hugokernel/Bleuette/export/img/BleuettePi_board.png

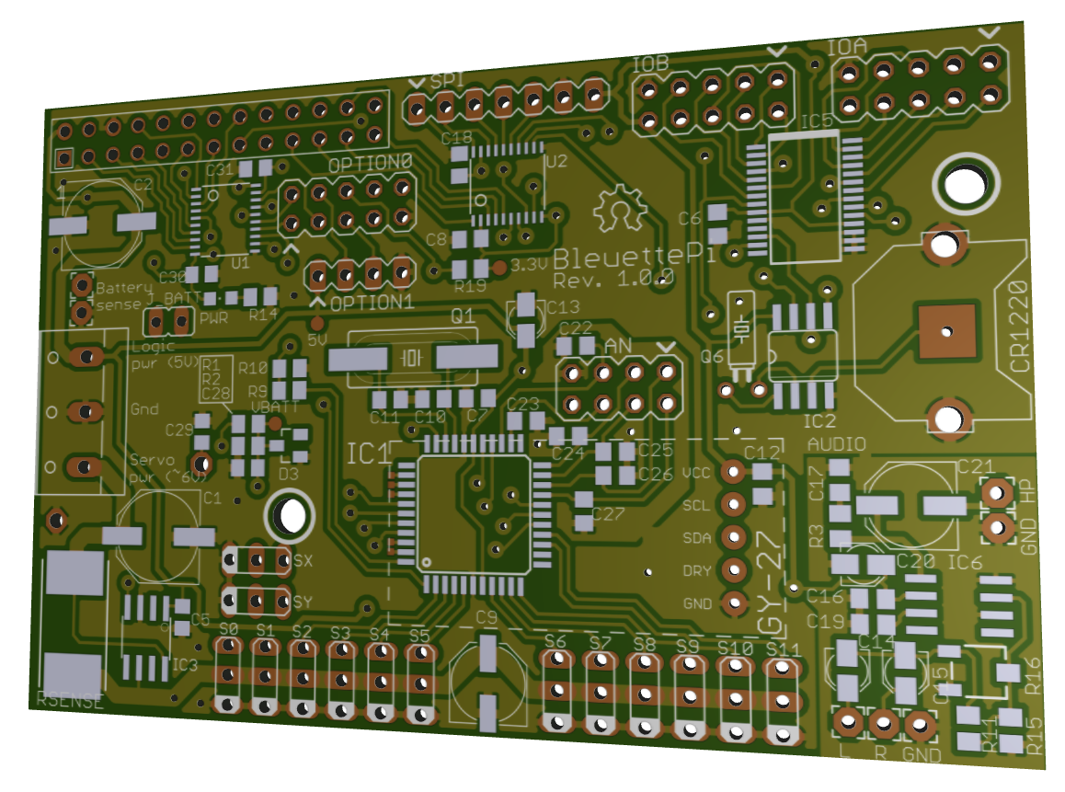
export/img/BleuettePi_board.png
