hugokernel/Bleuette/export/img/BleuettePi_pcb.png

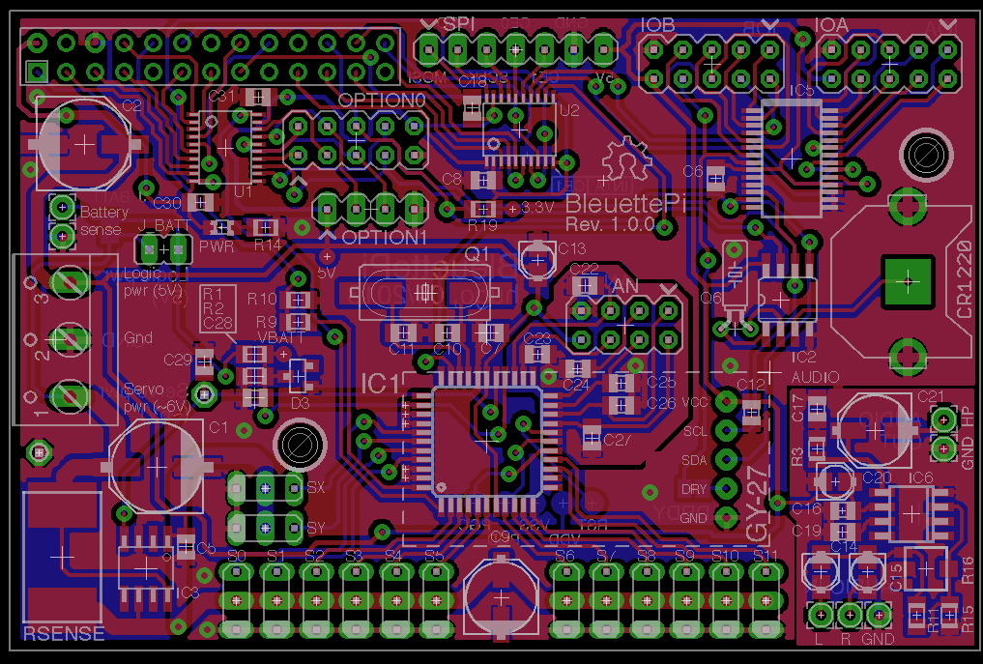
export/img/BleuettePi_pcb.png
