hugokernel/Bleuette/export/img/body.png

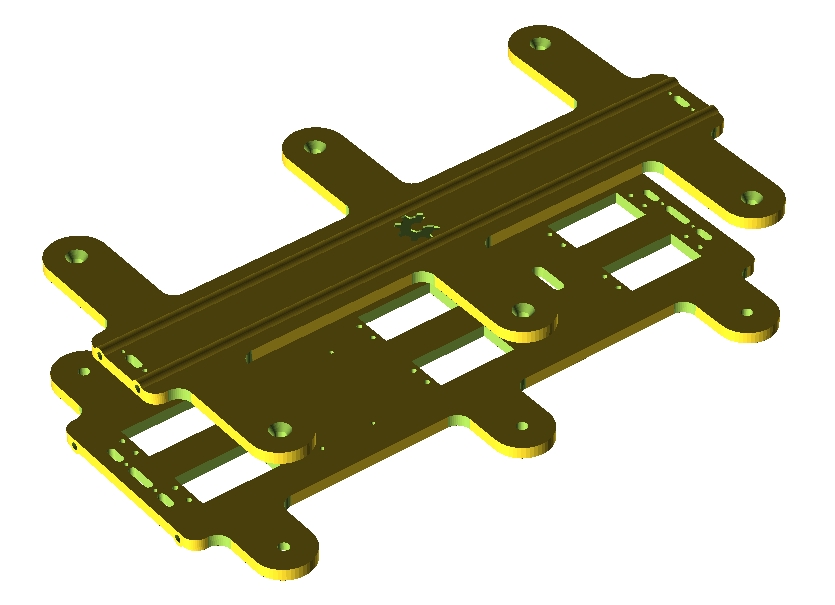
export/img/body.png
