hugokernel/Bleuette/export/img/body_base.png

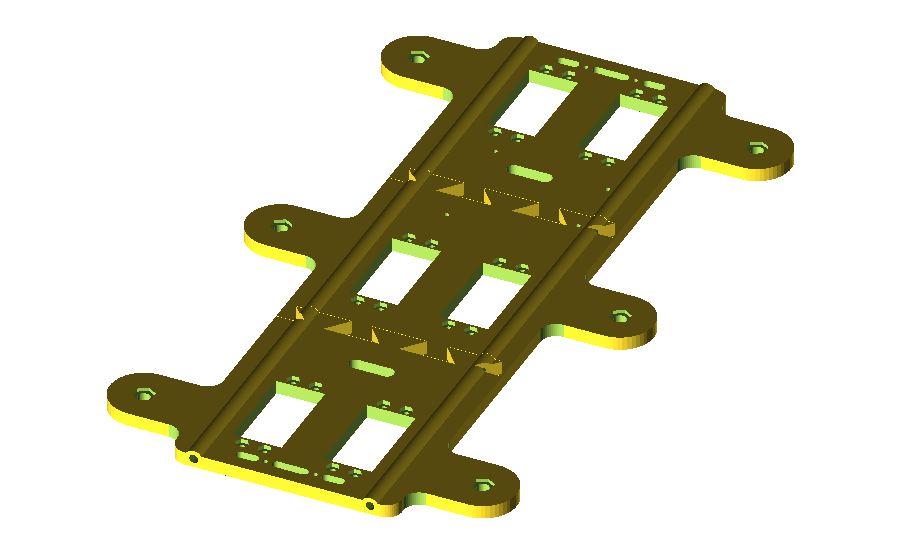
export/img/body_base.png
