hugokernel/Bleuette/export/img/body_base_ortho.png

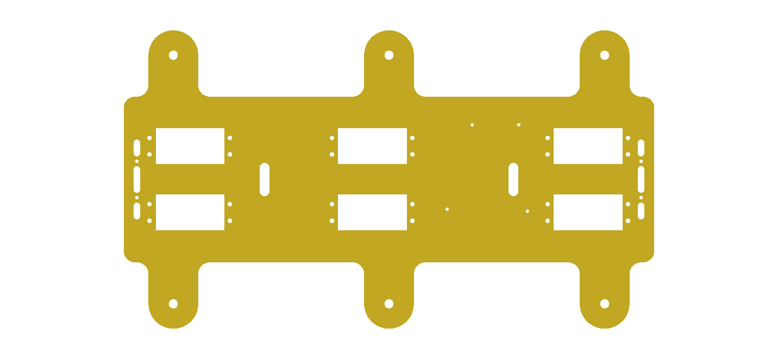
export/img/body_base_ortho.png
