hugokernel/Bleuette/export/img/body_support.png

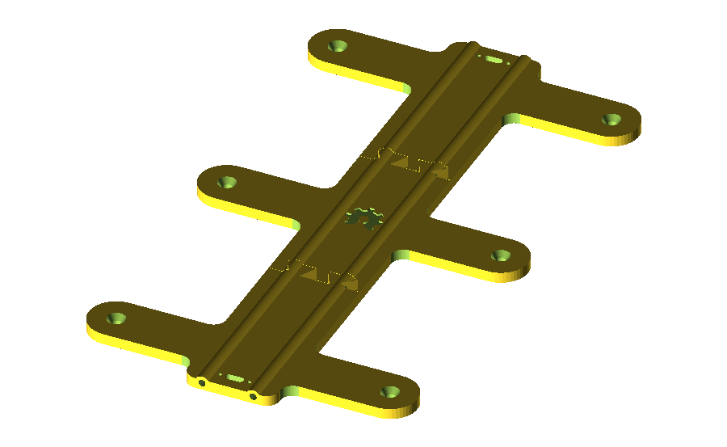
export/img/body_support.png
