hugokernel/Bleuette/export/img/body_support_ortho.png

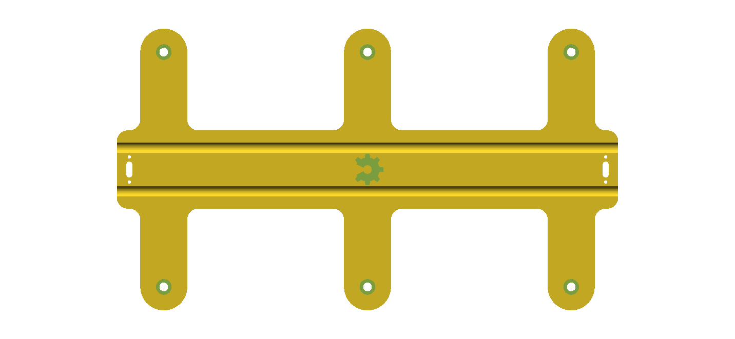
export/img/body_support_ortho.png
