hugokernel/Bleuette/export/img/elec_board.png

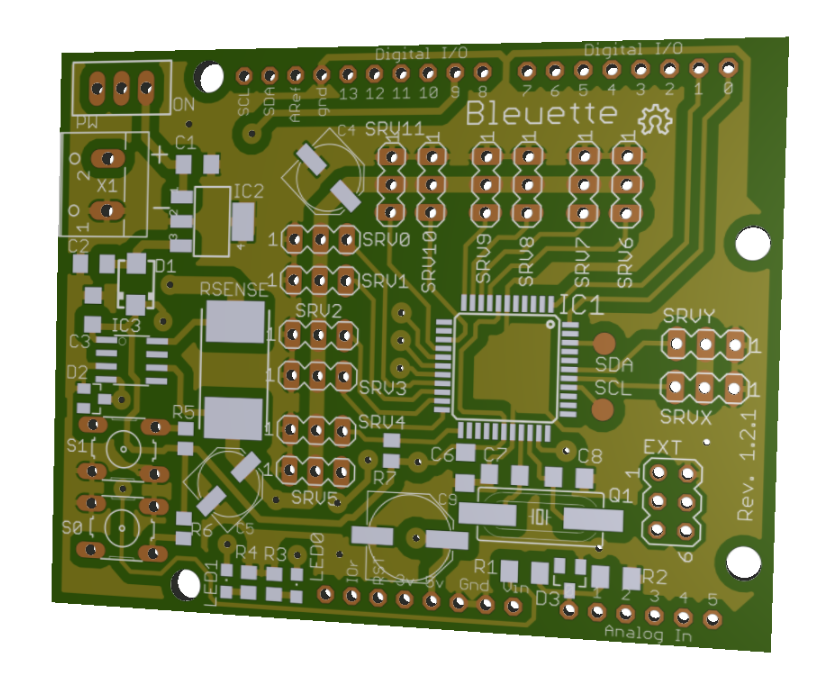
export/img/elec_board.png
