hugokernel/Bleuette/export/img/elec_board_1.2.1.png

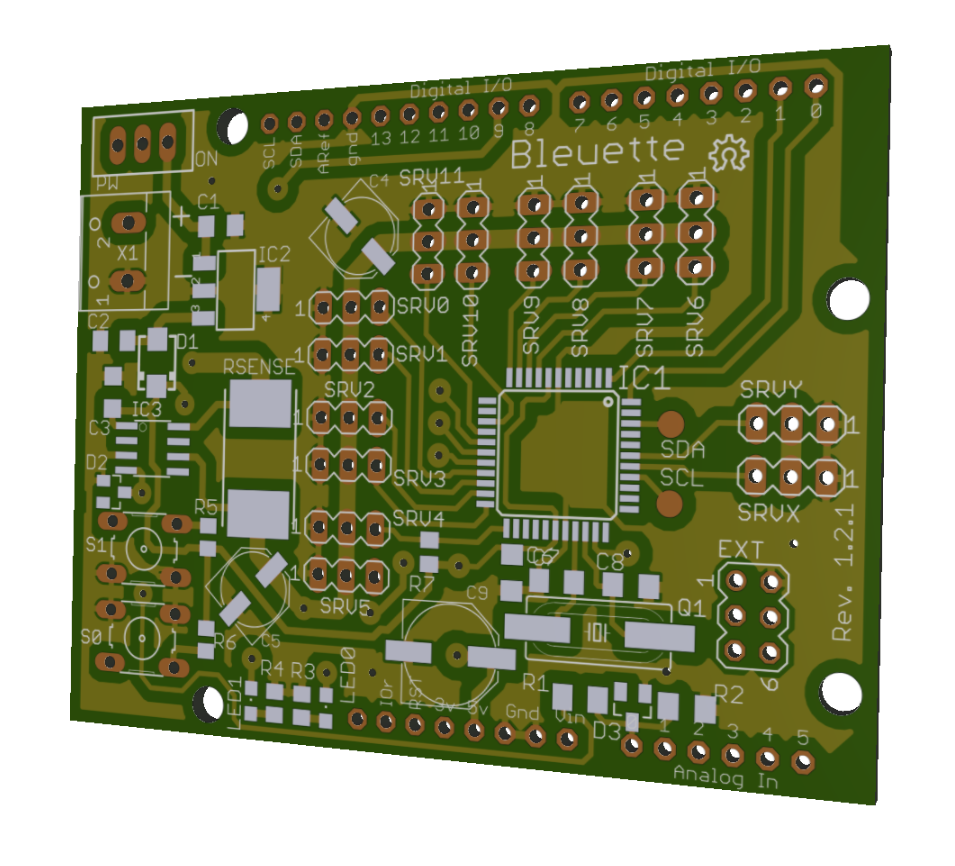
export/img/elec_board_1.2.1.png
