hugokernel/Bleuette/export/img/elec_pcb.png

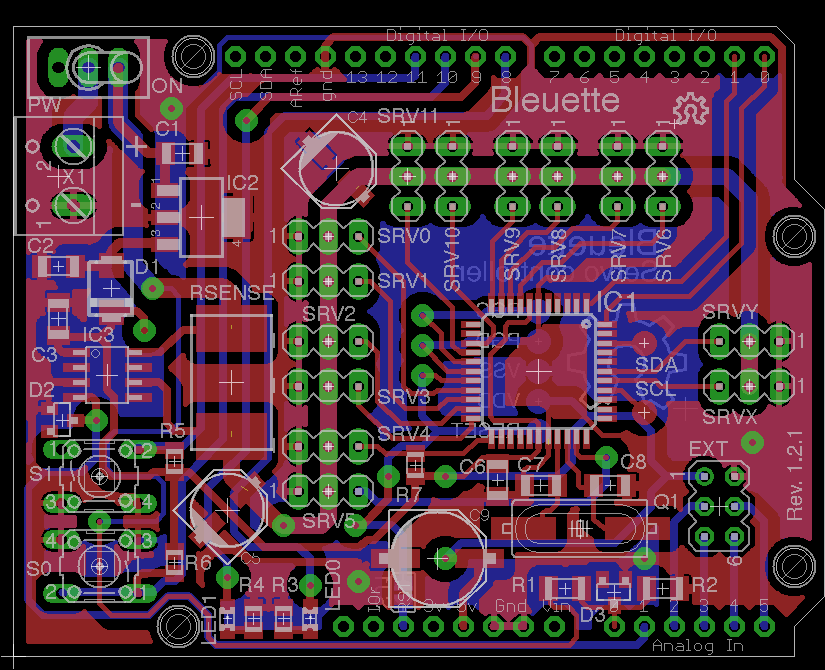
export/img/elec_pcb.png
