hugokernel/Bleuette/export/img/leg_holder.png

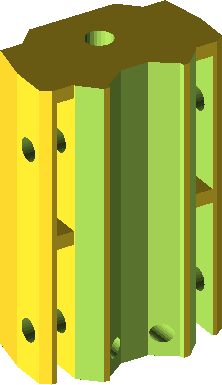
export/img/leg_holder.png
