hugokernel/Bleuette/export/img/leg_holder_pieces.png

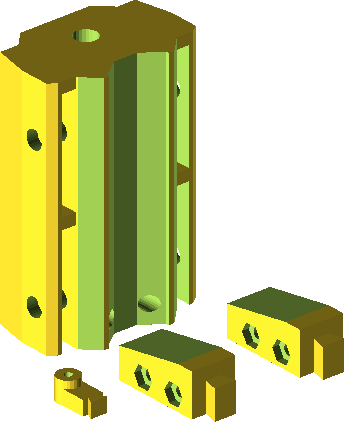
export/img/leg_holder_pieces.png
