hugokernel/Bleuette/export/img/leg_long.png

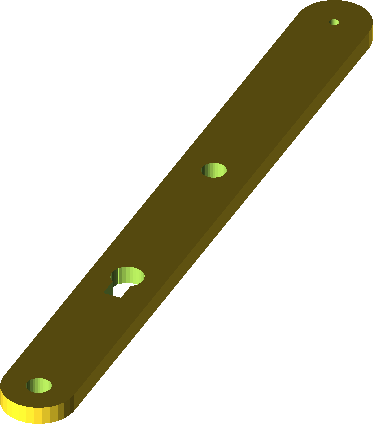
export/img/leg_long.png
