hugokernel/Bleuette/export/img/leg_main.png

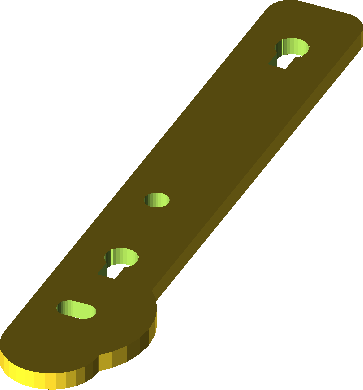
export/img/leg_main.png
