hugokernel/Bleuette/export/img/leg_sensor.png

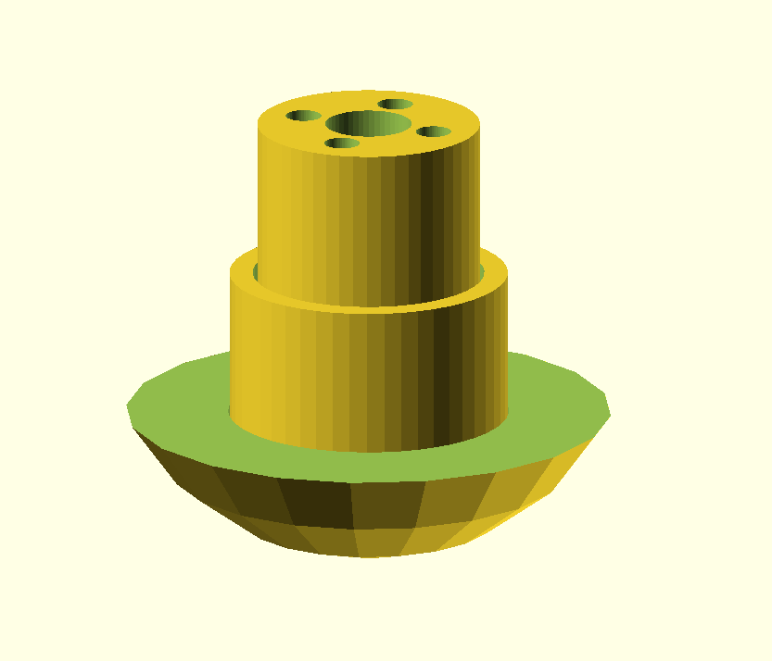
export/img/leg_sensor.png
