hugokernel/Bleuette/export/img/leg_short.png

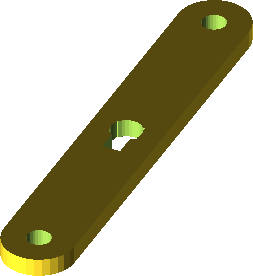
export/img/leg_short.png
