hugokernel/Bleuette/export/img/pcb_1.0.2/00.jpeg

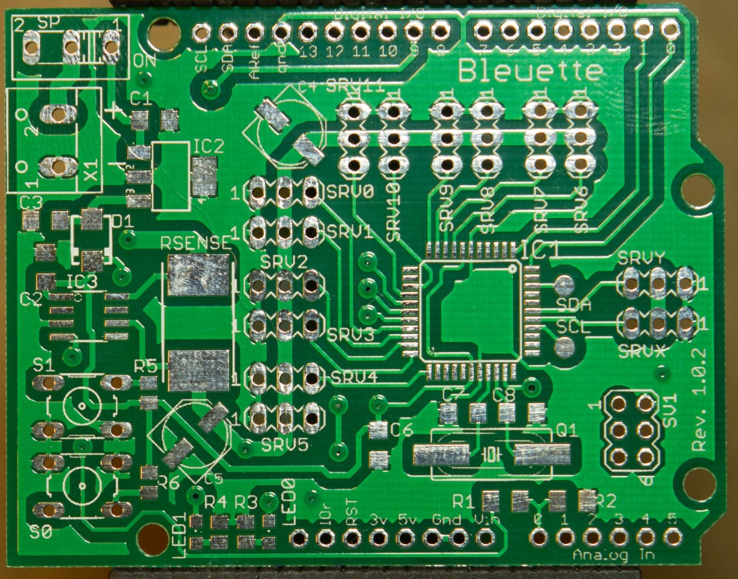
export/img/pcb_1.0.2/00.jpeg
