hugokernel/Bleuette/export/img/pcb_1.0.2/03.jpeg

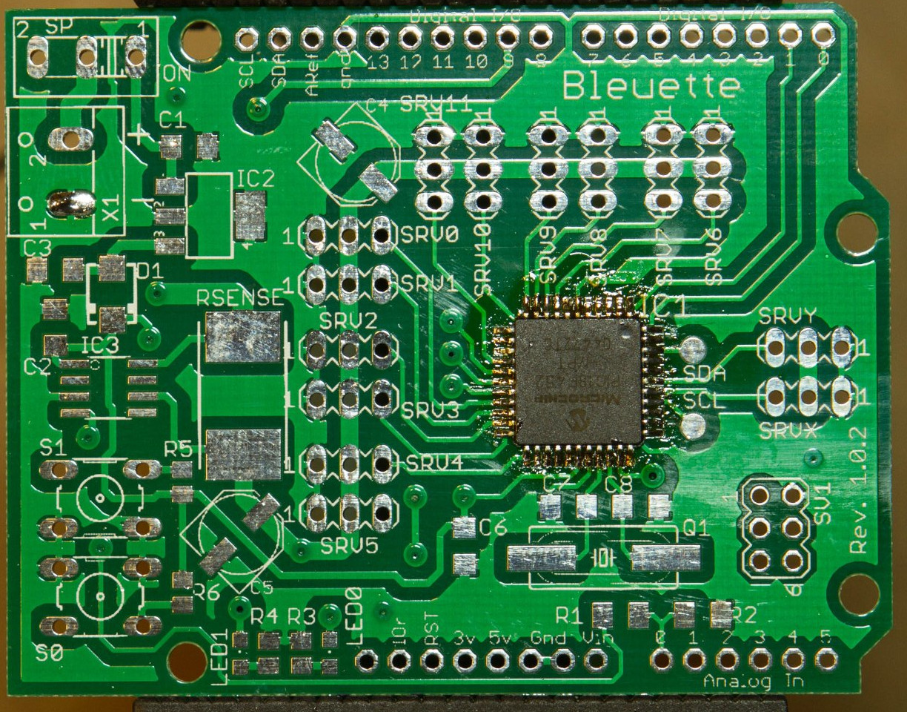
export/img/pcb_1.0.2/03.jpeg
