hugokernel/Bleuette/export/img/pcb_1.0.2/04.jpeg

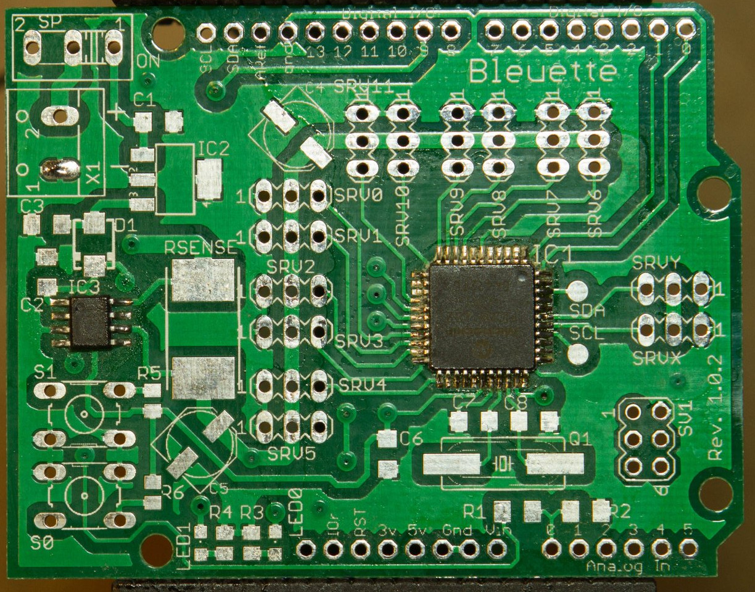
export/img/pcb_1.0.2/04.jpeg
