hugokernel/Bleuette/export/img/pcb_1.0.2/05.jpeg

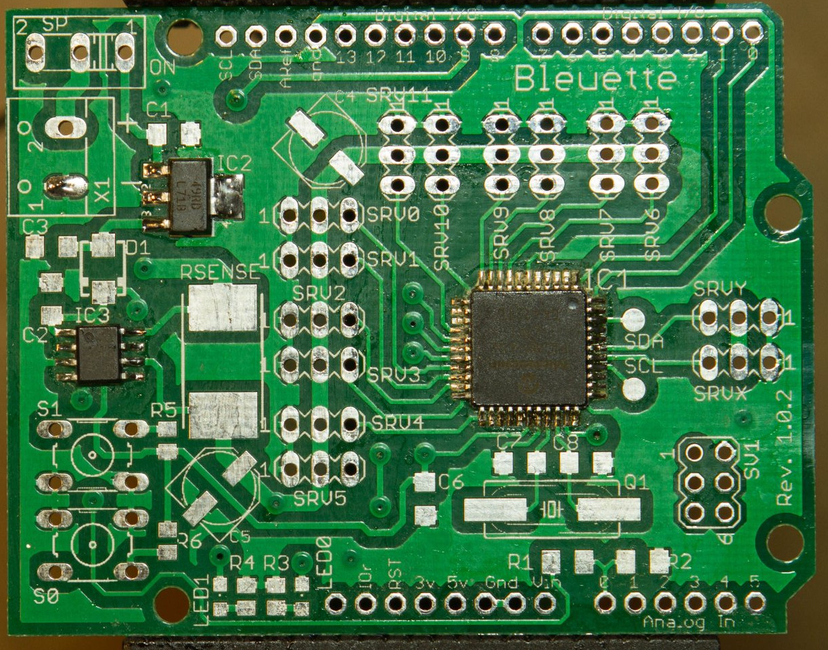
export/img/pcb_1.0.2/05.jpeg
