hugokernel/Bleuette/export/img/pcb_1.0.2/07.jpeg

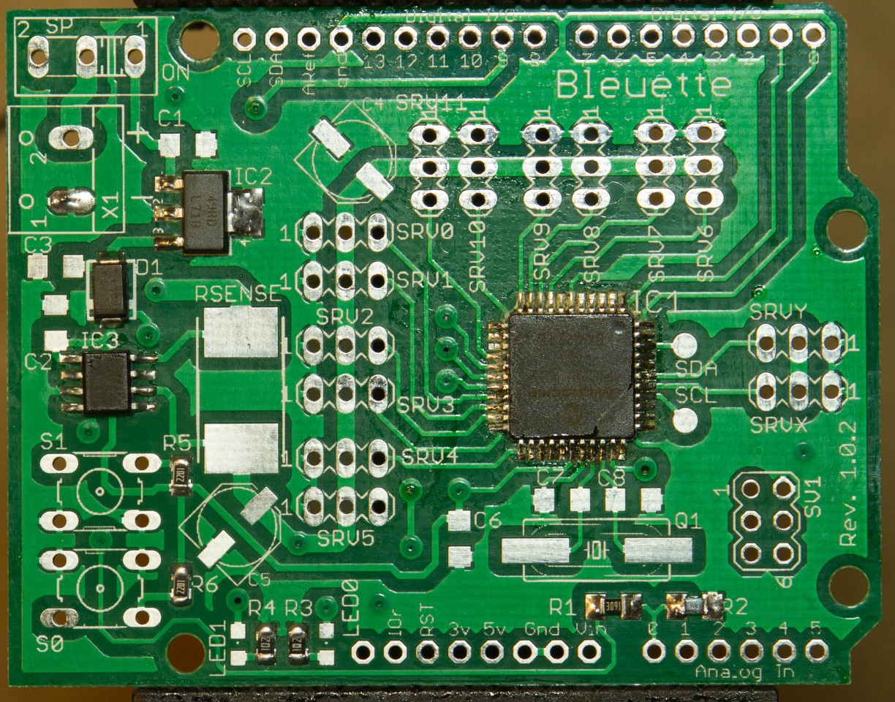
export/img/pcb_1.0.2/07.jpeg
