hugokernel/Bleuette/export/img/pcb_1.0.2/08.jpeg

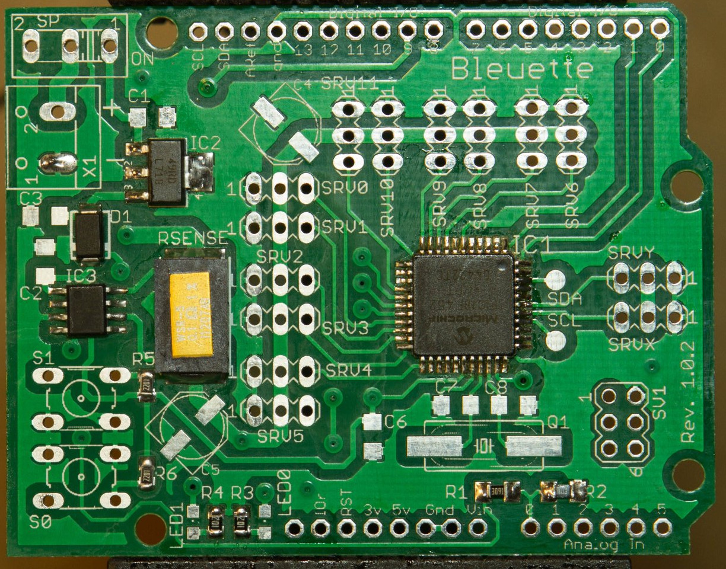
export/img/pcb_1.0.2/08.jpeg
