hugokernel/Bleuette/export/img/pcb_1.0.2/11.jpeg

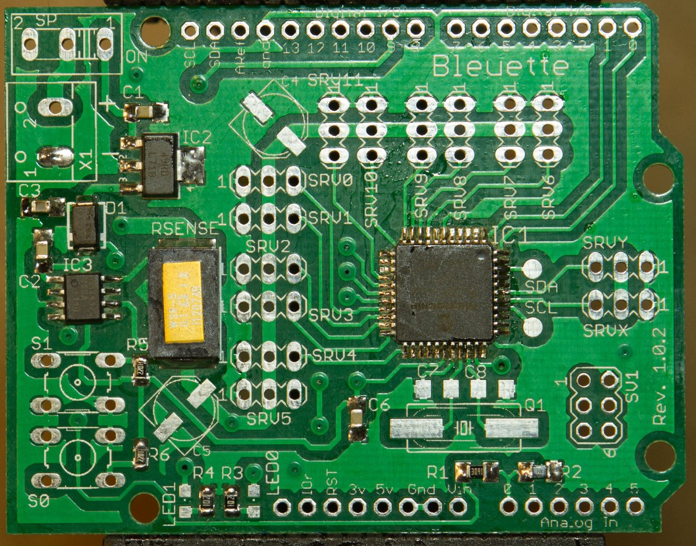
export/img/pcb_1.0.2/11.jpeg
