hugokernel/Bleuette/export/img/pcb_1.0.2/12.jpeg

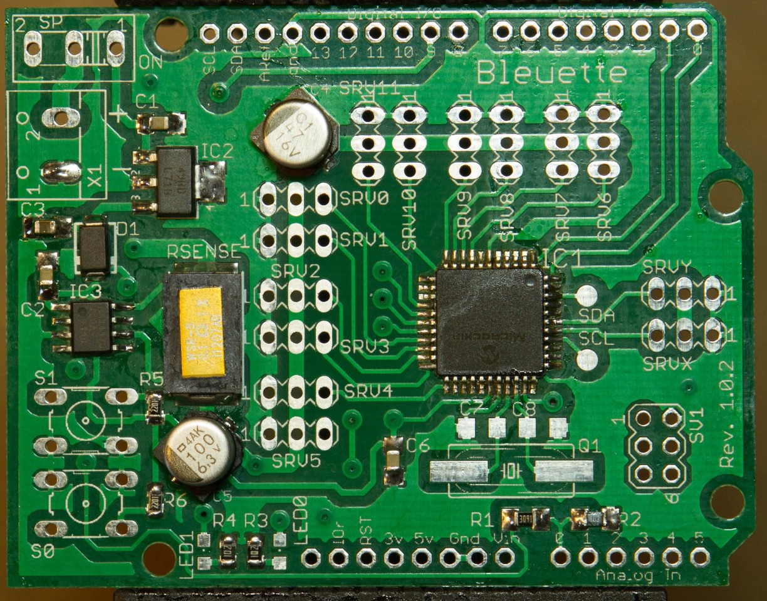
export/img/pcb_1.0.2/12.jpeg
