hugokernel/Bleuette/export/img/pcb_1.0.2/14.jpeg

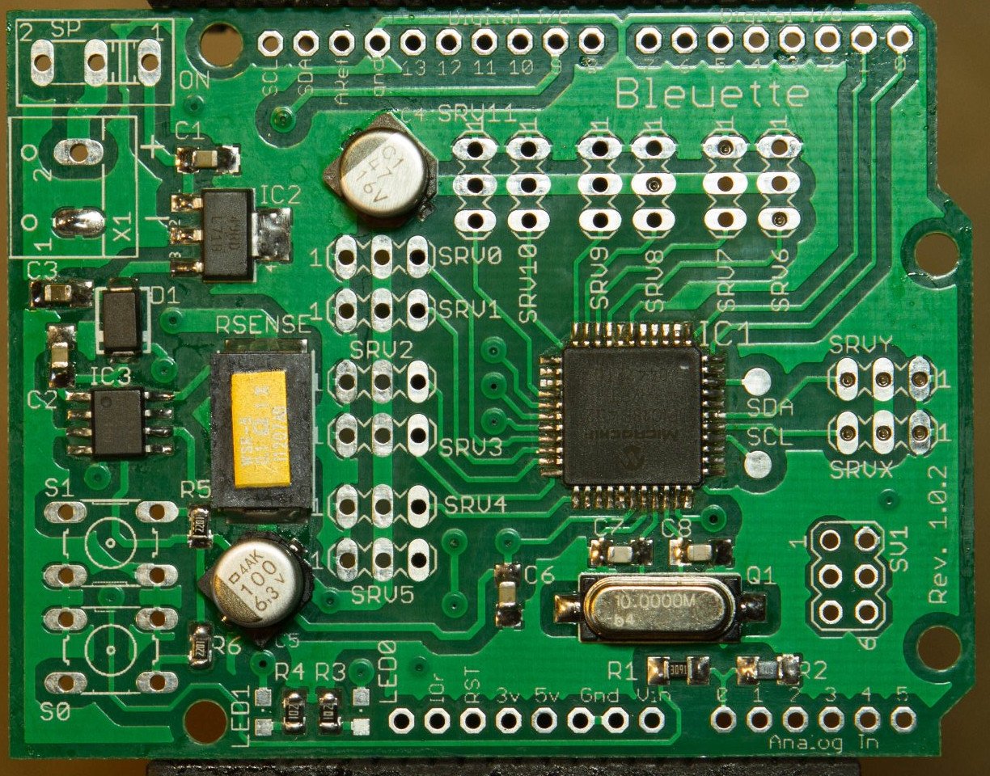
export/img/pcb_1.0.2/14.jpeg
