hugokernel/Bleuette/export/img/pcb_1.0.2/15.jpeg

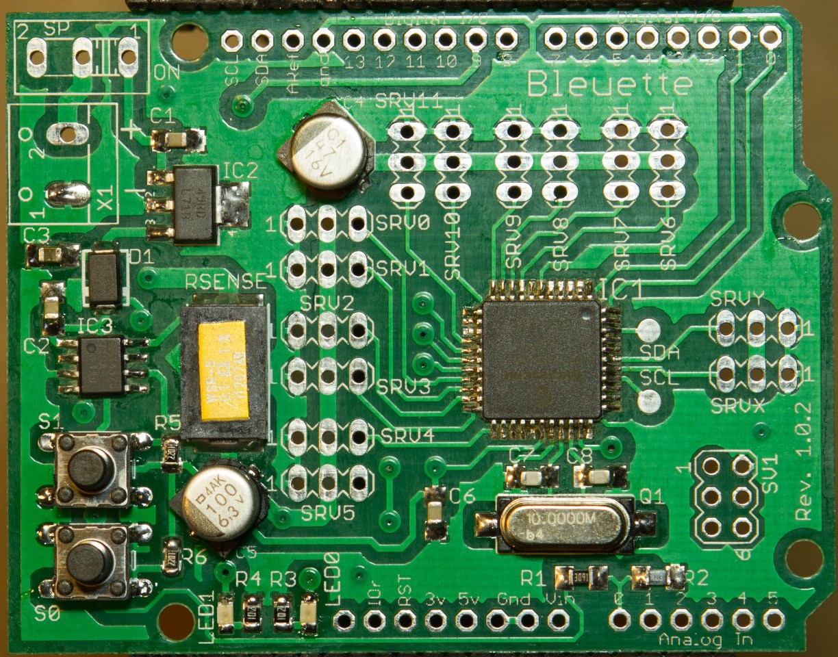
export/img/pcb_1.0.2/15.jpeg
