hugokernel/Bleuette/export/img/pcb_1.0.2/17.jpeg

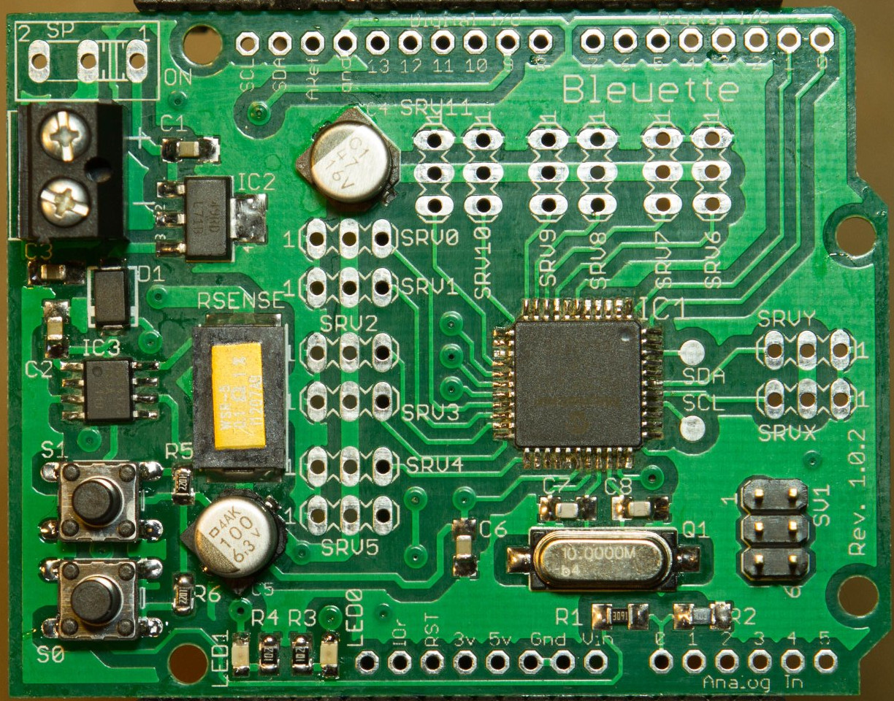
export/img/pcb_1.0.2/17.jpeg
