hugokernel/Bleuette/export/img/pcb_1.0.2/18.jpeg

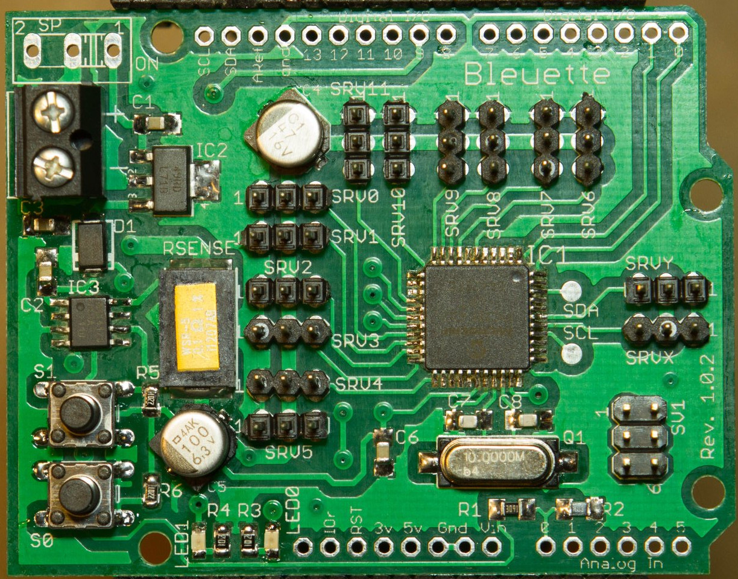
export/img/pcb_1.0.2/18.jpeg
