hugokernel/Bleuette/export/img/pcb_1.0.2/19.jpeg

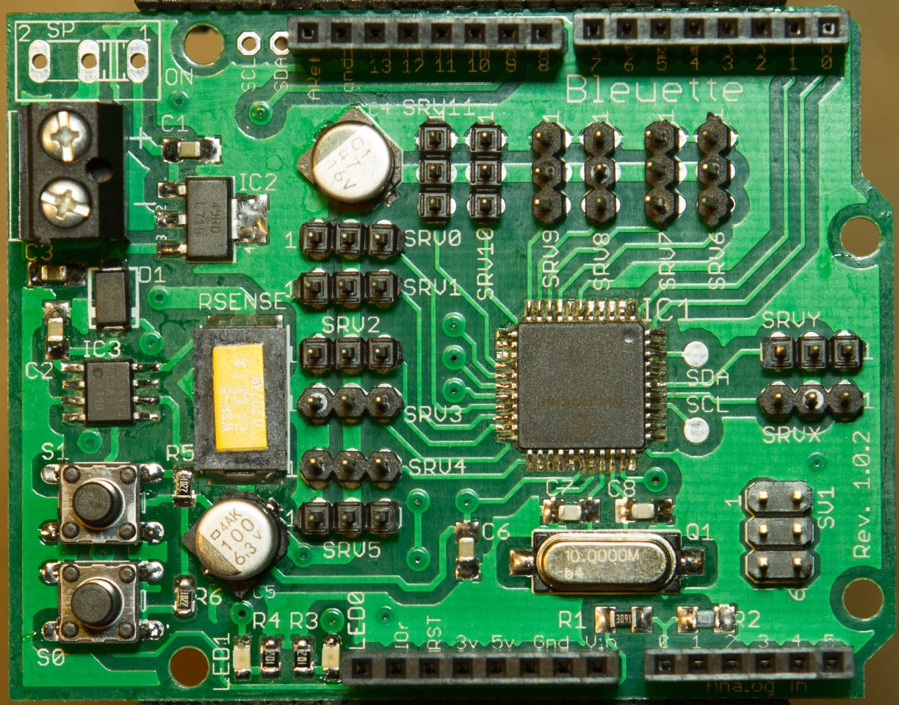
export/img/pcb_1.0.2/19.jpeg
