hugokernel/Bleuette/export/img/pcb_1.0.2/20.jpeg

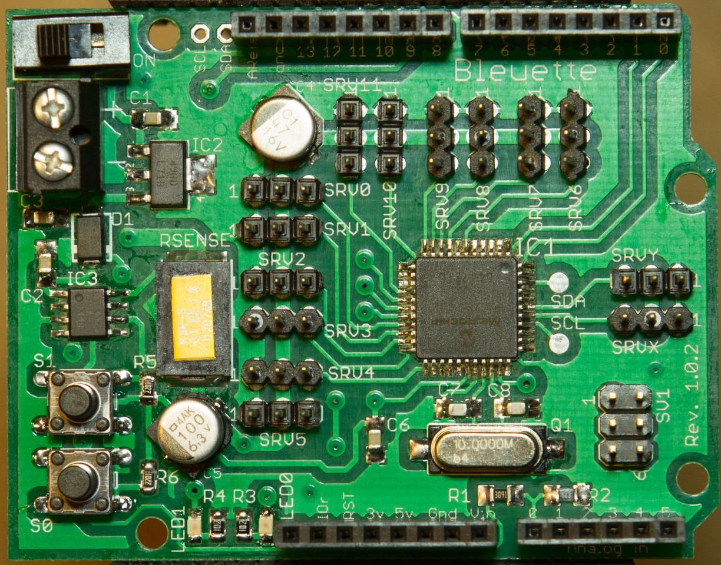
export/img/pcb_1.0.2/20.jpeg
