hugokernel/Bleuette/export/img/pcb_1.0.2/21.jpeg

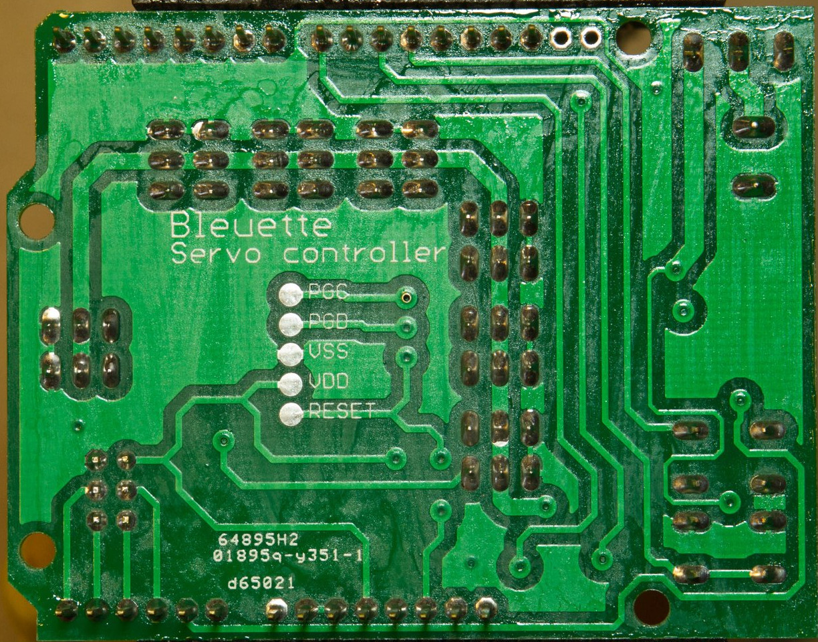
export/img/pcb_1.0.2/21.jpeg
