hugokernel/Bleuette/export/img/pcb_1.0.2/thumbs/09.jpeg

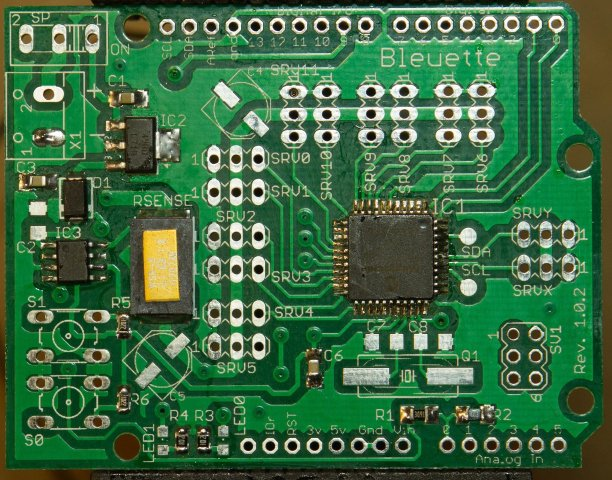
export/img/pcb_1.0.2/thumbs/09.jpeg
