hugokernel/Bleuette/export/img/rudder.png

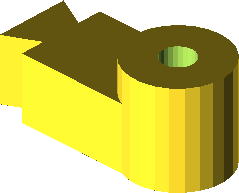
export/img/rudder.png
