hugokernel/Bleuette/export/img/servo_holder.png

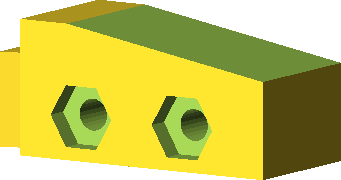
export/img/servo_holder.png
