hugokernel/Bleuette/export/img/spring.png

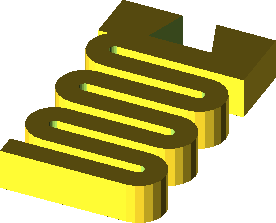
export/img/spring.png
