hugokernel/Bleuette/export/img/thumbs/body_support_ortho.png

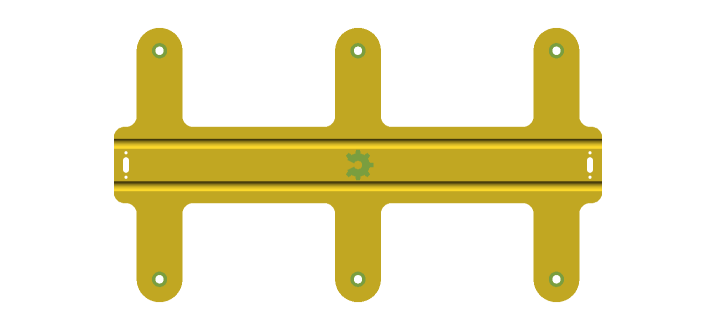
export/img/thumbs/body_support_ortho.png
