hugokernel/Bleuette/export/stl/oshw_logo.stl

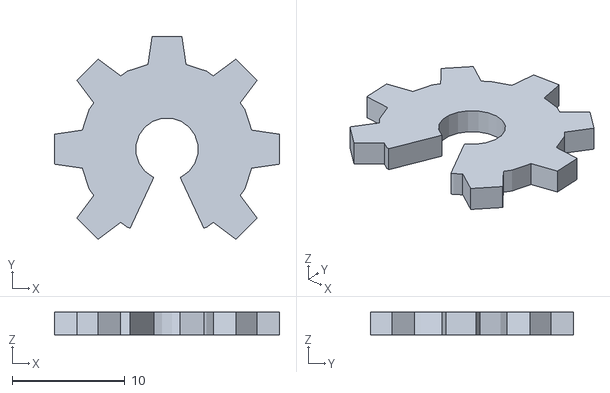
[picture p67: CAD file, 2012-10-22]
export/stl/oshw_logo.stl
20.0 x 18.0 x 2.00
