hugokernel/Bleuette/export/stl/body_1_top.stl

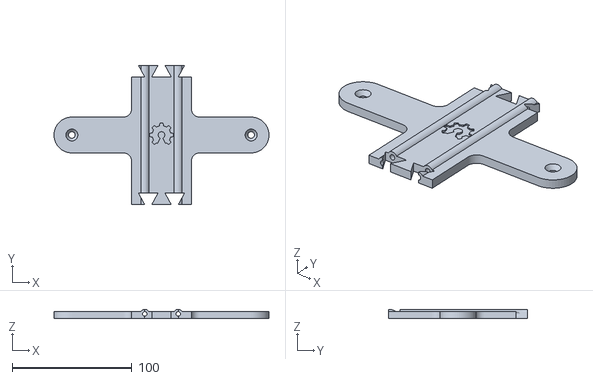
[picture p68: CAD file, 2012-09-28]
export/stl/body_1_top.stl
179.9 x 116.1 x 7.90
