hugokernel/Bleuette/export/stl/body_1_bottom.stl

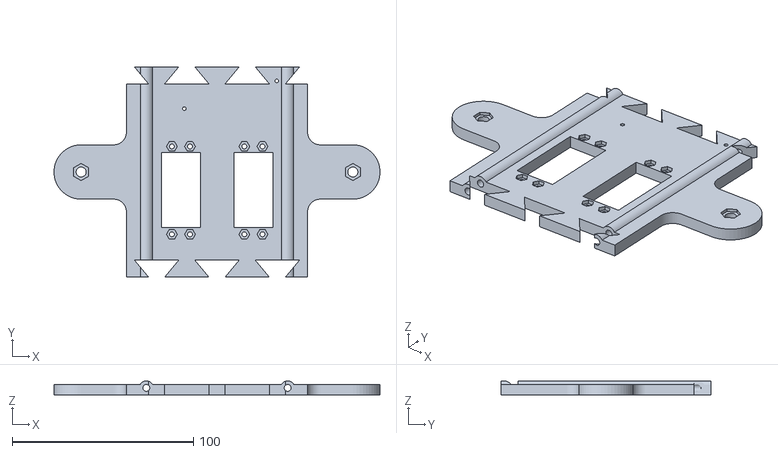
[picture p69: CAD file, 2012-09-28]
export/stl/body_1_bottom.stl
179.9 x 116.1 x 7.90
