hugokernel/Bleuette/export/stl/body_2_bottom.stl

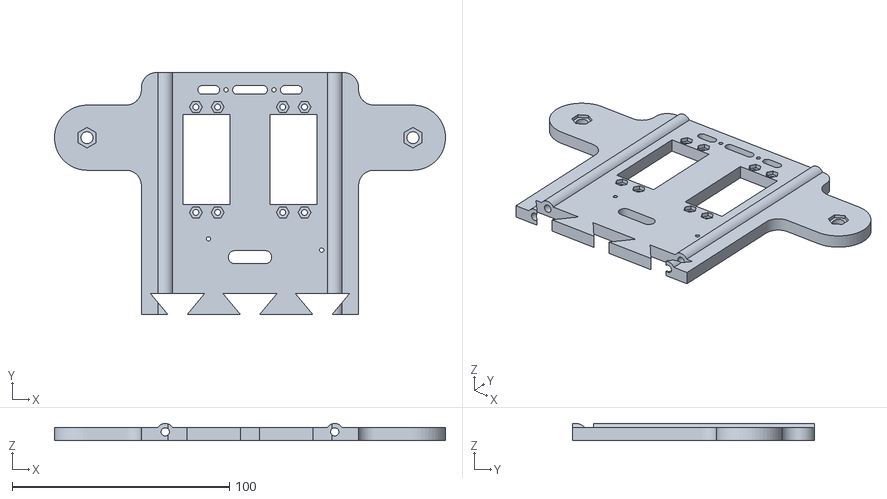
[picture p70: CAD file, 2012-09-28]
export/stl/body_2_bottom.stl
179.9 x 111.4 x 7.90
