hugokernel/Bleuette/export/stl/body_2_top.stl

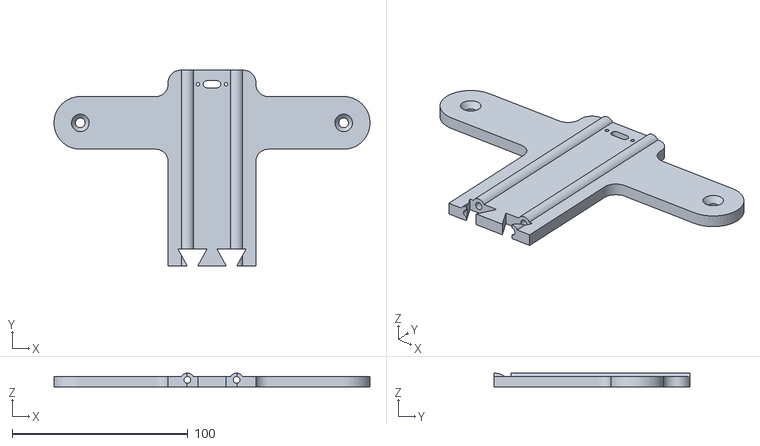
[picture p71: CAD file, 2012-09-28]
export/stl/body_2_top.stl
179.9 x 111.4 x 7.90
