hugokernel/Bleuette/src/Bleuette/bleuette.h

/*
    Bleuette.h Control Bleuette shield
    Copyright (c) 2013 Charles Rincheval.  All rights reserved.

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
    The latest version of this library can always be found at
    http://www.digitalspirit.org/
*/

#ifndef Bleuette_h
#define Bleuette_h

#include <wiring.h>
#include <Arduino.h>

//#include "HardwareSerial.h"
#include <servocontroller.h>

#define BLEUETTE_LED0   8
#define BLEUETTE_LED1   9

#define BLEUETTE_BUTTON0    10
#define BLEUETTE_BUTTON1    11

#define LED0    BLEUETTE_LED0
#define LED1    BLEUETTE_LED1
#define BUTTON0 BLEUETTE_BUTTON0
#define BUTTON1 BLEUETTE_BUTTON1

typedef struct motion_t {
    unsigned long delay;        // How much time
    unsigned long servos;       // Servo bits field
    unsigned char count;        // Values count
    char values[14];            // All values for each servo
};

typedef struct sequence_t {
    bool loopable;              // Sequence is loopable ?
    unsigned int count;         // Motion count
    motion_t *motion;           // Motion struct
};

class Bleuette
{
private:

public:
    ServoController _servo;
    Bleuette();

    void init(void);

    void ledOn(unsigned char);
    void ledOff(unsigned char);

    bool getButtonState(unsigned char);

    int getVoltage();
    int getCurrent();

    // Walk
    bool runSequence(struct sequence_t);
};

Bleuette::Bleuette()
{
    pinMode(BLEUETTE_LED0, OUTPUT);
    pinMode(BLEUETTE_LED1, OUTPUT);
}

void Bleuette::init(void)
{
    _servo = ServoController();
    _servo.init();
}

/**
 *  Led on !
 */
void Bleuette::ledOn(unsigned char led)
{
    digitalWrite(led, HIGH);
}

/**
 *  Led off !
 */
void Bleuette::ledOff(unsigned char led)
{
    digitalWrite(led, LOW);
}

/**
 *  Get button status
 */
bool Bleuette::getButtonState(unsigned char button)
{
    return digitalRead(button);
}

/**
 *  Get voltage
 */
int Bleuette::getVoltage()
{
    return analogRead(0);
}

/**
 *  Get voltage
 */
int Bleuette::getCurrent()
{
    return analogRead(1);
}

/**
 *  Run walk sequence
 */
bool Bleuette::runSequence(struct sequence_t seq) {
    for (unsigned int i = 0; i < seq.count; i++) {
        _servo.setValues(seq.motion[i].servos, seq.motion[i].values, seq.motion[i].count);
        _servo.sendValues();
        delay(seq.motion[i].delay);
    }
}

#endif
